tim-eastwood/rii-518bt-usb-qmk-pcb/kicad/keyboard-usb.kicad_sch

## KiCad design kicad/keyboard-usb.kicad_sch (2025-06-24)

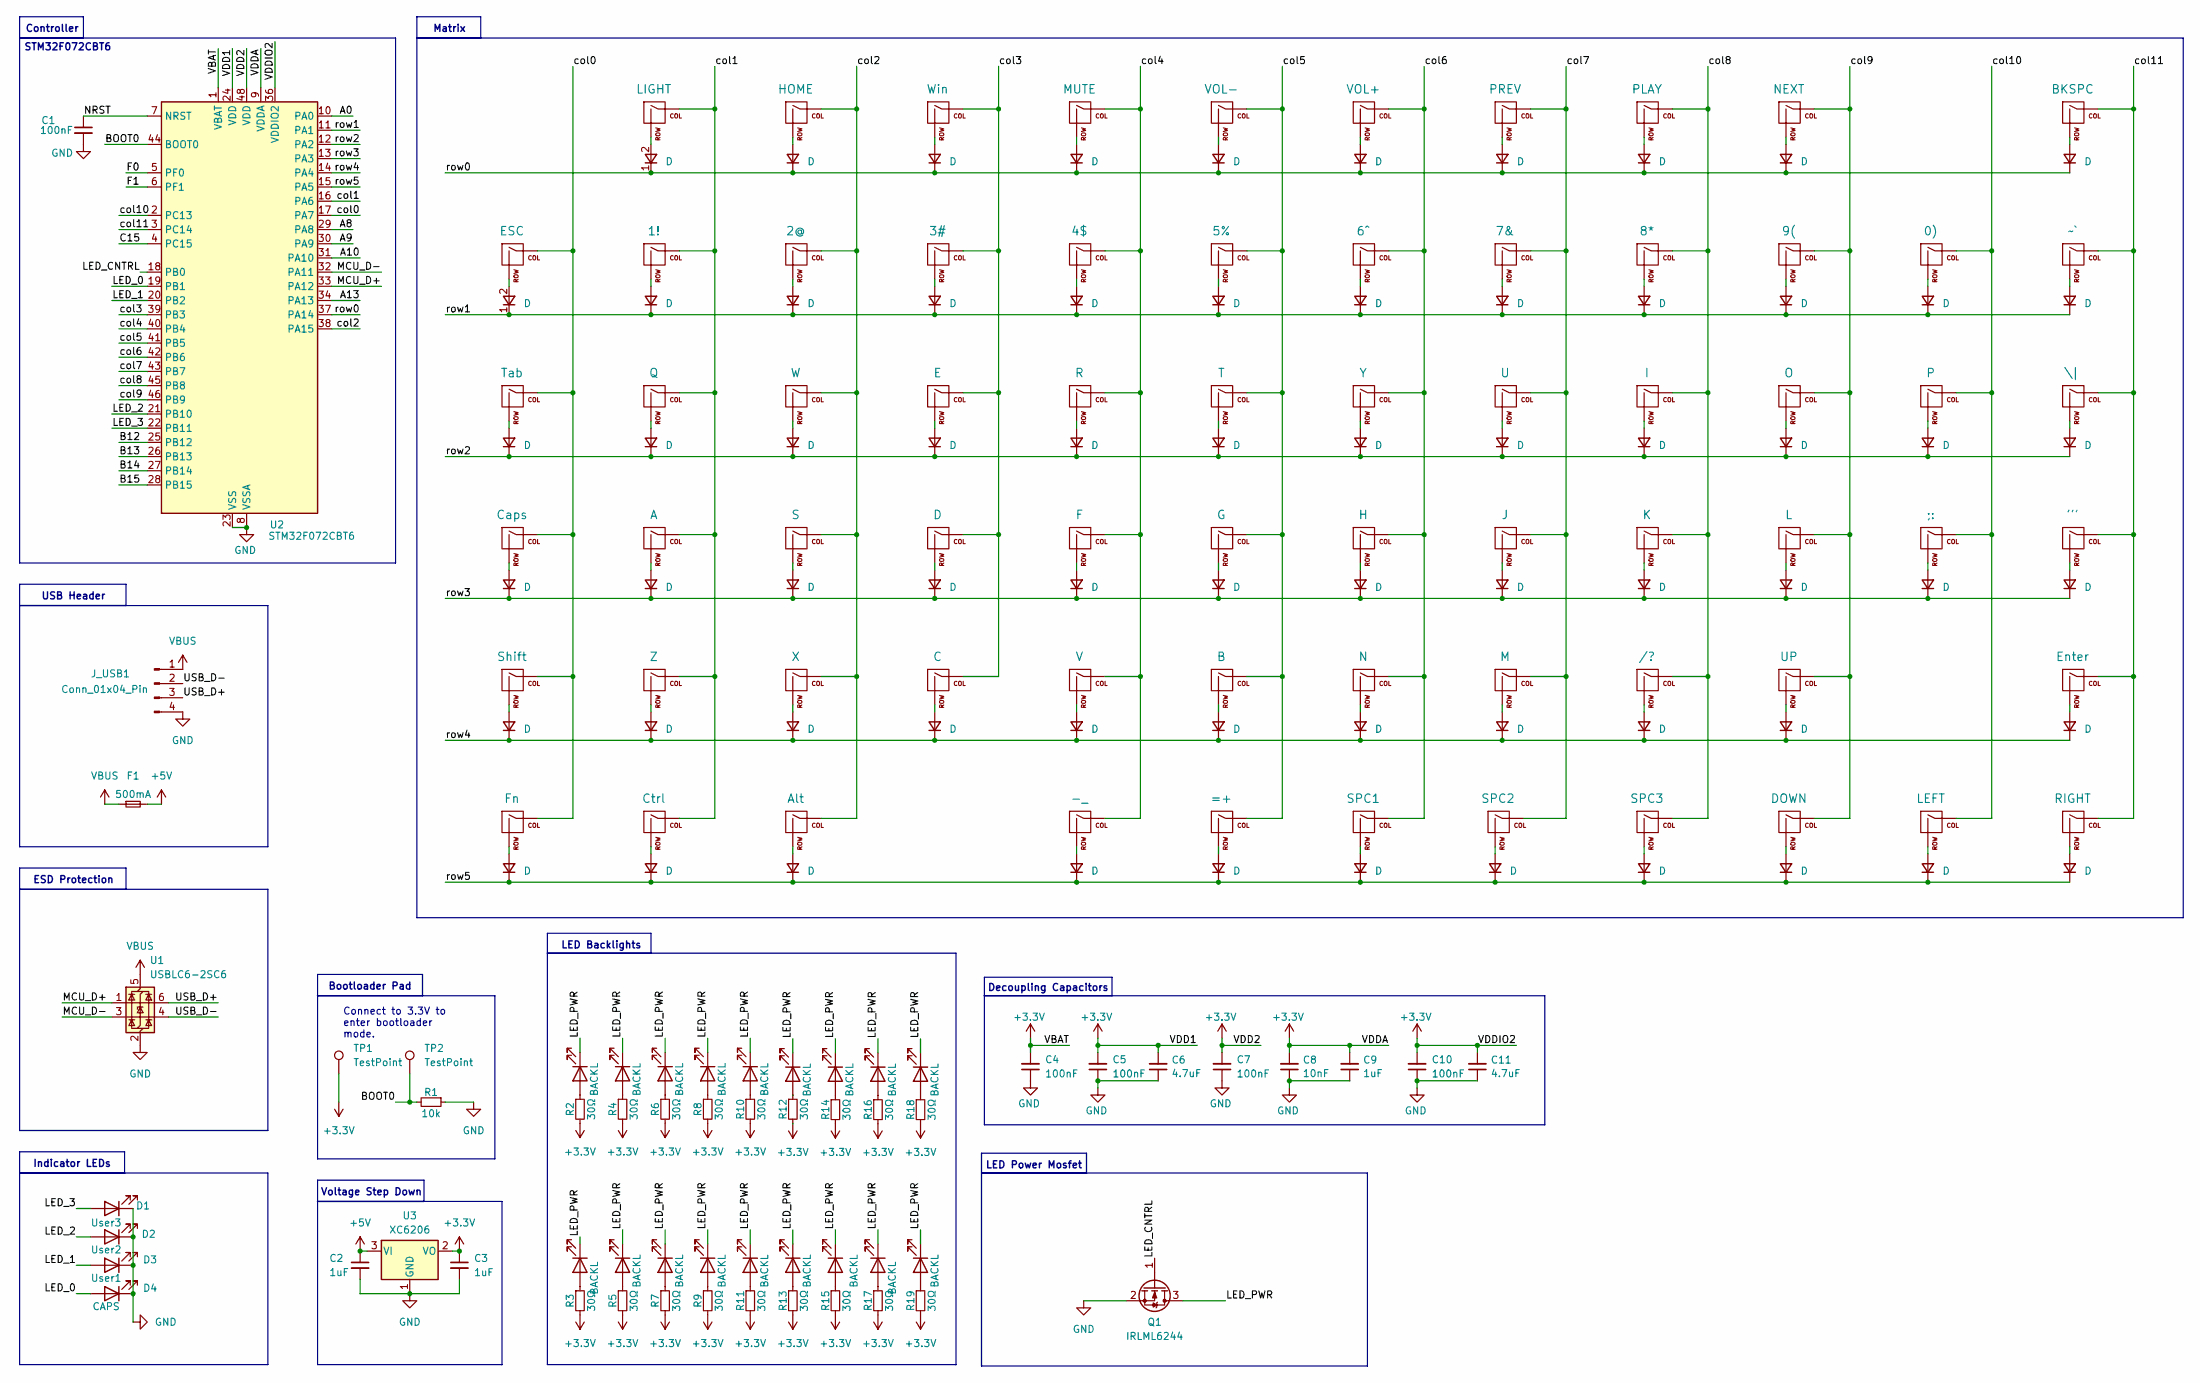
[picture p3: schematic keyboard-usb.kicad_sch]

Parts:
C1: 100nF; C_0402_1005Metric; LCSC C307331
C2, C3: 1uF; C_0402_1005Metric; LCSC C52923
C4, C5, C7, C10: 100nF; C_0402_1005Metric; MPN CL05B104KB54PNC; LCSC C307331
C6, C11: 4.7uF; C_0402_1005Metric; MPN CL05A475MP5NRNC; LCSC C23733
C8: 10nF; C_0402_1005Metric; MPN CL05B103KB5NNNC; LCSC C15195
C9: 1uF; C_0402_1005Metric; MPN CL05A105KA5NQNC; LCSC C52923
D1: User3; LED_0402_1005Metric; LCSC C883173
D2: User2; LED_0402_1005Metric; LCSC C883173
D3: User1; LED_0402_1005Metric; LCSC C883173
D4: CAPS; LED_0402_1005Metric; LCSC C883173
D5, D6, D7, D8, D9, D10, D11, D12, D13, D14, D15, D16, D17, D18, D19, D20, D21, D22: BACKL; LED_0402_1005Metric; LCSC C883173
D_1, D_2, D_3, D_4, D_5, D_6, D_7, D_8, D_9, D_10, D_11, D_12, D_13, D_14, D_15, D_16, D_17, D_18, D_19, D_20, D_21, D_22, D_23, D_24, D_25, D_26, D_27, D_28, D_29, D_30, D_31, D_32, D_33, D_34, D_35, D_36, D_37, D_38, D_39, D_40, D_41, D_42, D_43, D_44, D_45, D_46, D_47, D_48, D_49, D_50, D_51, D_52, D_53, D_54, D_55, D_56, D_57, D_58, D_59, D_60, D_61, D_62, D_63, D_64, D_65, D_66, D_67, D_68: D; D_SOD-523; LCSC C5345964
F1: 500mA; Fuse_0603_1608Metric; LCSC C210357
J_USB1: Conn_01x04_Pin; Pads_1x04_P2.54mm_SMD
K_1: ESC; dome-tactile-pad
K_2: Tab; dome-tactile-pad
K_3: Caps; dome-tactile-pad
K_4: Shift; dome-tactile-pad
K_5: Fn; dome-tactile-pad
K_6: LIGHT; dome-tactile-pad
K_7: 1!; dome-tactile-pad
K_8: Q; dome-tactile-pad
K_9: A; dome-tactile-pad
K_10: Z; dome-tactile-pad
K_11: Ctrl; dome-tactile-pad
K_12: HOME; dome-tactile-pad
K_13: 2@; dome-tactile-pad
K_14: W; dome-tactile-pad
K_15: S; dome-tactile-pad
K_16: X; dome-tactile-pad
K_17: Alt; dome-tactile-pad
K_18: Win; dome-tactile-pad
K_19: 3#; dome-tactile-pad
K_20: E; dome-tactile-pad
K_21: D; dome-tactile-pad
K_22: C; dome-tactile-pad
K_23: MUTE; dome-tactile-pad
K_24: 4$; dome-tactile-pad
K_25: R; dome-tactile-pad
K_26: F; dome-tactile-pad
K_27: V; dome-tactile-pad
K_28: -_; dome-tactile-pad
K_29: VOL-; dome-tactile-pad
K_30: 5%; dome-tactile-pad
K_31: T; dome-tactile-pad
K_32: G; dome-tactile-pad
K_33: B; dome-tactile-pad
K_34: =+; dome-tactile-pad
K_35: VOL+; dome-tactile-pad
K_36: 6^; dome-tactile-pad
K_37: Y; dome-tactile-pad
K_38: H; dome-tactile-pad
K_39: N; dome-tactile-pad
K_40: SPC1; dome-tactile-pad
K_41: SPC2; dome-tactile-pad
K_42: PREV; dome-tactile-pad
K_43: 7&; dome-tactile-pad
K_44: U; dome-tactile-pad
K_45: J; dome-tactile-pad
K_46: M; dome-tactile-pad
K_47: PLAY; dome-tactile-pad
K_48: 8*; dome-tactile-pad
K_49: I; dome-tactile-pad
K_50: K; dome-tactile-pad
K_51: /?; dome-tactile-pad
K_52: SPC3; dome-tactile-pad
K_53: NEXT; dome-tactile-pad
K_54: 9(; dome-tactile-pad
K_55: O; dome-tactile-pad
K_56: L; dome-tactile-pad
K_57: UP; dome-tactile-pad
K_58: DOWN; dome-tactile-pad
K_59: 0); dome-tactile-pad
K_60: P; dome-tactile-pad
K_61: ;:; dome-tactile-pad
K_62: LEFT; dome-tactile-pad
K_63: BKSPC; dome-tactile-pad
K_64: ~`; dome-tactile-pad
K_65: \|; dome-tactile-pad
K_66: '''; dome-tactile-pad
K_67: Enter; dome-tactile-pad
K_68: RIGHT; dome-tactile-pad
Q1: IRLML6244; SOT-23; LCSC C5364313
R1: 10k; R_0402_1005Metric; LCSC C25744
R2, R3, R4, R5, R6, R7, R8, R9, R10, R11, R12, R13, R14, R15, R16, R17, R18, R19: 30Ω; R_0402_1005Metric; LCSC C1091
TP1, TP2: TestPoint; TestPoint_Pad_D1.5mm
U1: USBLC6-2SC6; SOT-23-6; LCSC C2827654
U2: STM32F072CBT6; LQFP-48_7x7mm_P0.5mm; LCSC C81720
U3: XC6206; SOT-23; LCSC C5446

Connections:
+3.3V: C3.1, C4.2, C5.2, C6.2, C7.2, C8.2, C9.2, C10.2, C11.2, R2.2, R3.2, R4.2, R5.2, R6.2, R7.2, R8.2, R9.2, R10.2, R11.2, R12.2, R13.2, R14.2, R15.2, R16.2, R17.2, R18.2, R19.2, TP1.1, U2.1 (VBAT), U2.9 (VDDA), U2.24 (VDD), U2.36 (VDDIO2), U2.48 (VDD), U3.2 (VO)
+5V: C2.1, F1.2, U3.3 (VI)
A0: U2.10 (PA0)
A8: U2.29 (PA8)
A9: U2.30 (PA9)
A10: U2.31 (PA10)
A13: U2.34 (PA13)
B12: U2.25 (PB12)
B13: U2.26 (PB13)
B14: U2.27 (PB14)
B15: U2.28 (PB15)
BOOT0: R1.2, TP2.1, U2.44 (BOOT0)
C15: U2.4 (PC15)
F0: U2.5 (PF0)
F1: U2.6 (PF1)
GND: C1.2, C2.2, C3.2, C4.1, C5.1, C6.1, C7.1, C8.1, C9.1, C10.1, C11.1, D1.1 (K), D2.1 (K), D3.1 (K), D4.1 (K), J_USB1.4, Q1.2 (S), R1.1, U1.2 (GND), U2.8 (VSSA), U2.23 (VSS), U2.35 (VSS), U2.47 (VSS), U3.1 (GND)
LED_0: D4.2 (A), U2.19 (PB1)
LED_1: D3.2 (A), U2.20 (PB2)
LED_2: D2.2 (A), U2.21 (PB10)
LED_3: D1.2 (A), U2.22 (PB11)
LED_CNTRL: Q1.1 (G), U2.18 (PB0)
LED_PWR: D5.1 (K), D6.1 (K), D7.1 (K), D8.1 (K), D9.1 (K), D10.1 (K), D11.1 (K), D12.1 (K), D13.1 (K), D14.1 (K), D15.1 (K), D16.1 (K), D17.1 (K), D18.1 (K), D19.1 (K), D20.1 (K), D21.1 (K), D22.1 (K), Q1.3 (D)
MCU_D+: U1.1 (I/O1), U2.33 (PA12)
MCU_D-: U1.3 (I/O2), U2.32 (PA11)
NRST: C1.1, U2.7 (NRST)
unnamed: D5.2 (A), R2.1
unnamed: D6.2 (A), R3.1
unnamed: D7.2 (A), R4.1
unnamed: D8.2 (A), R5.1
unnamed: D9.2 (A), R6.1
unnamed: D10.2 (A), R7.1
unnamed: D11.2 (A), R8.1
unnamed: D12.2 (A), R9.1
unnamed: D13.2 (A), R10.1
unnamed: D14.2 (A), R11.1
unnamed: D15.2 (A), R12.1
unnamed: D16.2 (A), R13.1
unnamed: D17.2 (A), R14.1
unnamed: D18.2 (A), R15.1
unnamed: D19.2 (A), R16.1
unnamed: D20.2 (A), R17.1
unnamed: D21.2 (A), R18.1
unnamed: D22.2 (A), R19.1
unnamed: D_1.2 (A), K_1.2 (ROW)
unnamed: D_2.2 (A), K_2.2 (ROW)
unnamed: D_3.2 (A), K_3.2 (ROW)
unnamed: D_4.2 (A), K_4.2 (ROW)
unnamed: D_5.2 (A), K_5.2 (ROW)
unnamed: D_6.2 (A), K_6.2 (ROW)
unnamed: D_7.2 (A), K_7.2 (ROW)
unnamed: D_8.2 (A), K_8.2 (ROW)
unnamed: D_9.2 (A), K_9.2 (ROW)
unnamed: D_10.2 (A), K_10.2 (ROW)
unnamed: D_11.2 (A), K_11.2 (ROW)
unnamed: D_12.2 (A), K_12.2 (ROW)
unnamed: D_13.2 (A), K_13.2 (ROW)
unnamed: D_14.2 (A), K_14.2 (ROW)
unnamed: D_15.2 (A), K_15.2 (ROW)
unnamed: D_16.2 (A), K_16.2 (ROW)
unnamed: D_17.2 (A), K_17.2 (ROW)
unnamed: D_18.2 (A), K_18.2 (ROW)
unnamed: D_19.2 (A), K_19.2 (ROW)
unnamed: D_20.2 (A), K_20.2 (ROW)
unnamed: D_21.2 (A), K_21.2 (ROW)
unnamed: D_22.2 (A), K_22.2 (ROW)
unnamed: D_23.2 (A), K_23.2 (ROW)
unnamed: D_24.2 (A), K_24.2 (ROW)
unnamed: D_25.2 (A), K_25.2 (ROW)
unnamed: D_26.2 (A), K_26.2 (ROW)
unnamed: D_27.2 (A), K_27.2 (ROW)
unnamed: D_28.2 (A), K_28.2 (ROW)
unnamed: D_29.2 (A), K_29.2 (ROW)
unnamed: D_30.2 (A), K_30.2 (ROW)
unnamed: D_31.2 (A), K_31.2 (ROW)
unnamed: D_32.2 (A), K_32.2 (ROW)
unnamed: D_33.2 (A), K_33.2 (ROW)
unnamed: D_34.2 (A), K_34.2 (ROW)
unnamed: D_35.2 (A), K_35.2 (ROW)
unnamed: D_36.2 (A), K_36.2 (ROW)
unnamed: D_37.2 (A), K_37.2 (ROW)
unnamed: D_38.2 (A), K_38.2 (ROW)
unnamed: D_39.2 (A), K_39.2 (ROW)
unnamed: D_40.2 (A), K_40.2 (ROW)
unnamed: D_41.2 (A), K_41.2 (ROW)
unnamed: D_42.2 (A), K_42.2 (ROW)
unnamed: D_43.2 (A), K_43.2 (ROW)
unnamed: D_44.2 (A), K_44.2 (ROW)
unnamed: D_45.2 (A), K_45.2 (ROW)
unnamed: D_46.2 (A), K_46.2 (ROW)
unnamed: D_47.2 (A), K_47.2 (ROW)
unnamed: D_48.2 (A), K_48.2 (ROW)
unnamed: D_49.2 (A), K_49.2 (ROW)
unnamed: D_50.2 (A), K_50.2 (ROW)
unnamed: D_51.2 (A), K_51.2 (ROW)
unnamed: D_52.2 (A), K_52.2 (ROW)
unnamed: D_53.2 (A), K_53.2 (ROW)
unnamed: D_54.2 (A), K_54.2 (ROW)
unnamed: D_55.2 (A), K_55.2 (ROW)
unnamed: D_56.2 (A), K_56.2 (ROW)
unnamed: D_57.2 (A), K_57.2 (ROW)
unnamed: D_58.2 (A), K_58.2 (ROW)
unnamed: D_59.2 (A), K_59.2 (ROW)
unnamed: D_60.2 (A), K_60.2 (ROW)
unnamed: D_61.2 (A), K_61.2 (ROW)
unnamed: D_62.2 (A), K_62.2 (ROW)
unnamed: D_63.2 (A), K_63.2 (ROW)
unnamed: D_64.2 (A), K_64.2 (ROW)
unnamed: D_65.2 (A), K_65.2 (ROW)
unnamed: D_66.2 (A), K_66.2 (ROW)
unnamed: D_67.2 (A), K_67.2 (ROW)
unnamed: D_68.2 (A), K_68.2 (ROW)
USB_D+: J_USB1.3, U1.6 (I/O1)
USB_D-: J_USB1.2, U1.4 (I/O2)
VBUS: F1.1, J_USB1.1, U1.5 (VBUS)
col0: K_1.1 (COL), K_2.1 (COL), K_3.1 (COL), K_4.1 (COL), K_5.1 (COL), U2.17 (PA7)
col1: K_6.1 (COL), K_7.1 (COL), K_8.1 (COL), K_9.1 (COL), K_10.1 (COL), K_11.1 (COL), U2.16 (PA6)
col2: K_12.1 (COL), K_13.1 (COL), K_14.1 (COL), K_15.1 (COL), K_16.1 (COL), K_17.1 (COL), U2.38 (PA15)
col3: K_18.1 (COL), K_19.1 (COL), K_20.1 (COL), K_21.1 (COL), K_22.1 (COL), U2.39 (PB3)
col4: K_23.1 (COL), K_24.1 (COL), K_25.1 (COL), K_26.1 (COL), K_27.1 (COL), K_28.1 (COL), U2.40 (PB4)
col5: K_29.1 (COL), K_30.1 (COL), K_31.1 (COL), K_32.1 (COL), K_33.1 (COL), K_34.1 (COL), U2.41 (PB5)
col6: K_35.1 (COL), K_36.1 (COL), K_37.1 (COL), K_38.1 (COL), K_39.1 (COL), K_40.1 (COL), U2.42 (PB6)
col7: K_41.1 (COL), K_42.1 (COL), K_43.1 (COL), K_44.1 (COL), K_45.1 (COL), K_46.1 (COL), U2.43 (PB7)
col8: K_47.1 (COL), K_48.1 (COL), K_49.1 (COL), K_50.1 (COL), K_51.1 (COL), K_52.1 (COL), U2.45 (PB8)
col9: K_53.1 (COL), K_54.1 (COL), K_55.1 (COL), K_56.1 (COL), K_57.1 (COL), K_58.1 (COL), U2.46 (PB9)
col10: K_59.1 (COL), K_60.1 (COL), K_61.1 (COL), K_62.1 (COL), U2.2 (PC13)
col11: K_63.1 (COL), K_64.1 (COL), K_65.1 (COL), K_66.1 (COL), K_67.1 (COL), K_68.1 (COL), U2.3 (PC14)
row0: D_6.1 (K), D_12.1 (K), D_18.1 (K), D_23.1 (K), D_29.1 (K), D_35.1 (K), D_42.1 (K), D_47.1 (K), D_53.1 (K), D_63.1 (K), U2.37 (PA14)
row1: D_1.1 (K), D_7.1 (K), D_13.1 (K), D_19.1 (K), D_24.1 (K), D_30.1 (K), D_36.1 (K), D_43.1 (K), D_48.1 (K), D_54.1 (K), D_59.1 (K), D_64.1 (K), U2.11 (PA1)
row2: D_2.1 (K), D_8.1 (K), D_14.1 (K), D_20.1 (K), D_25.1 (K), D_31.1 (K), D_37.1 (K), D_44.1 (K), D_49.1 (K), D_55.1 (K), D_60.1 (K), D_65.1 (K), U2.12 (PA2)
row3: D_3.1 (K), D_9.1 (K), D_15.1 (K), D_21.1 (K), D_26.1 (K), D_32.1 (K), D_38.1 (K), D_45.1 (K), D_50.1 (K), D_56.1 (K), D_61.1 (K), D_66.1 (K), U2.13 (PA3)
row4: D_4.1 (K), D_10.1 (K), D_16.1 (K), D_22.1 (K), D_27.1 (K), D_33.1 (K), D_39.1 (K), D_46.1 (K), D_51.1 (K), D_57.1 (K), D_67.1 (K), U2.14 (PA4)
row5: D_5.1 (K), D_11.1 (K), D_17.1 (K), D_28.1 (K), D_34.1 (K), D_40.1 (K), D_41.1 (K), D_52.1 (K), D_58.1 (K), D_62.1 (K), D_68.1 (K), U2.15 (PA5)

Notes on the sheet:
Matrix
Controller
STM32F072CBT6
Voltage Step Down
USB Header
Indicator LEDs
ESD Protection
Bootloader Pad
LED Power Mosfet
LED Backlights
Decoupling Capacitors
Connect to 3.3V to enter bootloader mode.
